RBEGamer/LixieClock/documentation/images/4_digit_complete.jpg

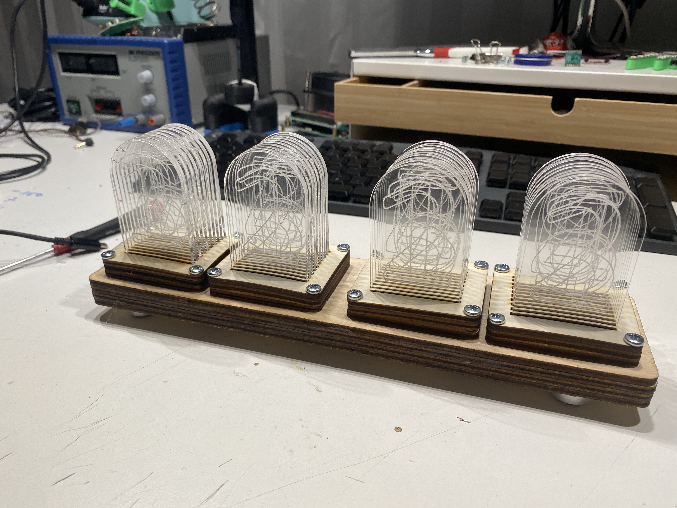
documentation/images/4_digit_complete.jpg
