RBEGamer/LixieClock/documentation/images/4_digit_on.jpg

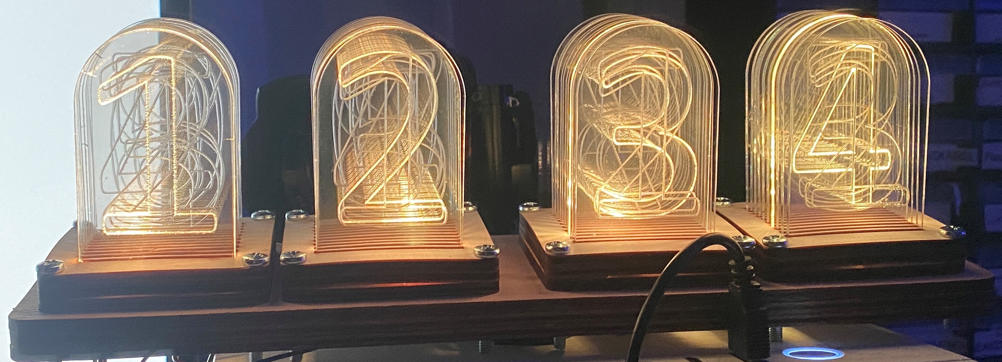
documentation/images/4_digit_on.jpg
