RBEGamer/LixieClock/documentation/images/2021-12-09 14.11.09.jpg

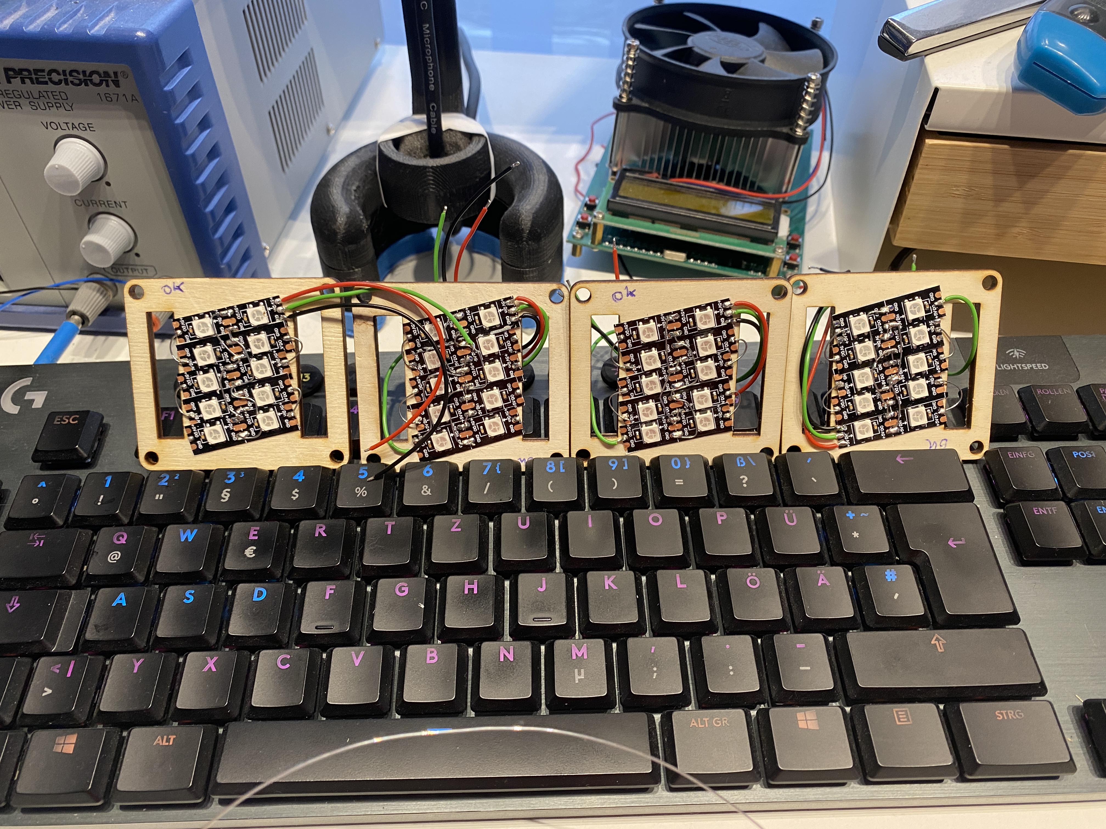
documentation/images/2021-12-09 14.11.09.jpg
