RBEGamer/LixieClock/documentation/images/2021-12-09 16.45.12-1.jpg

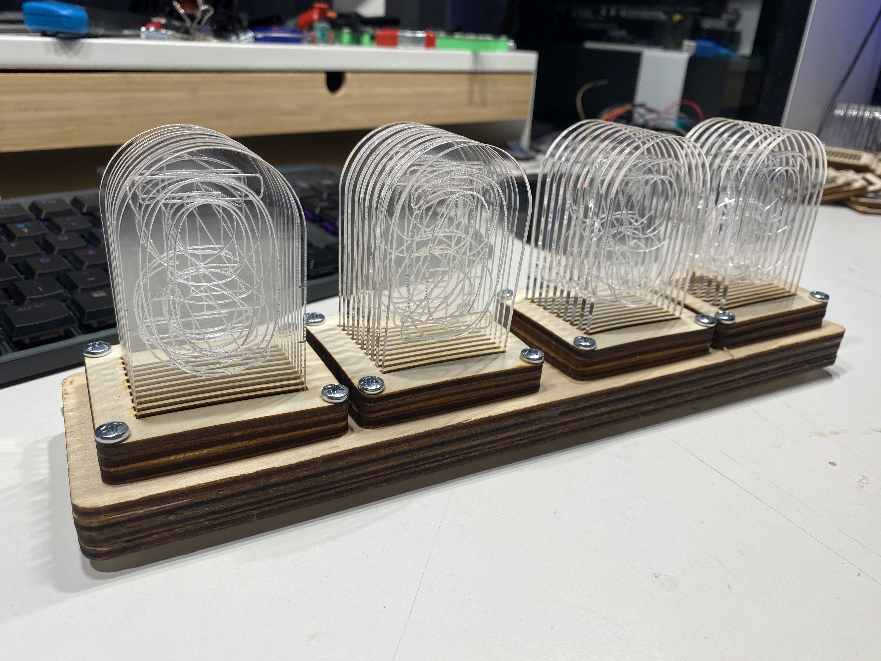
documentation/images/2021-12-09 16.45.12-1.jpg
