RBEGamer/LixieClock/documentation/images/2021-12-09 20.34.08.jpg

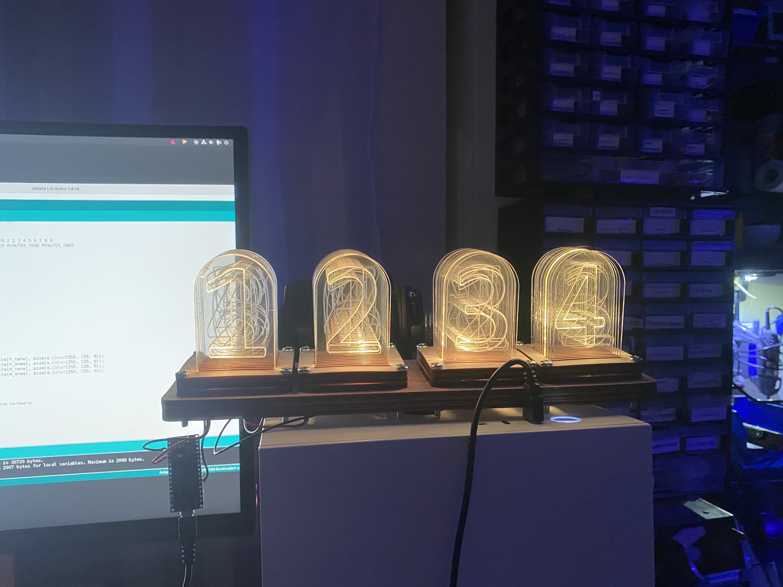
documentation/images/2021-12-09 20.34.08.jpg
