RBEGamer/LixieClock/documentation/images/2021-12-09 21.55.53.jpg

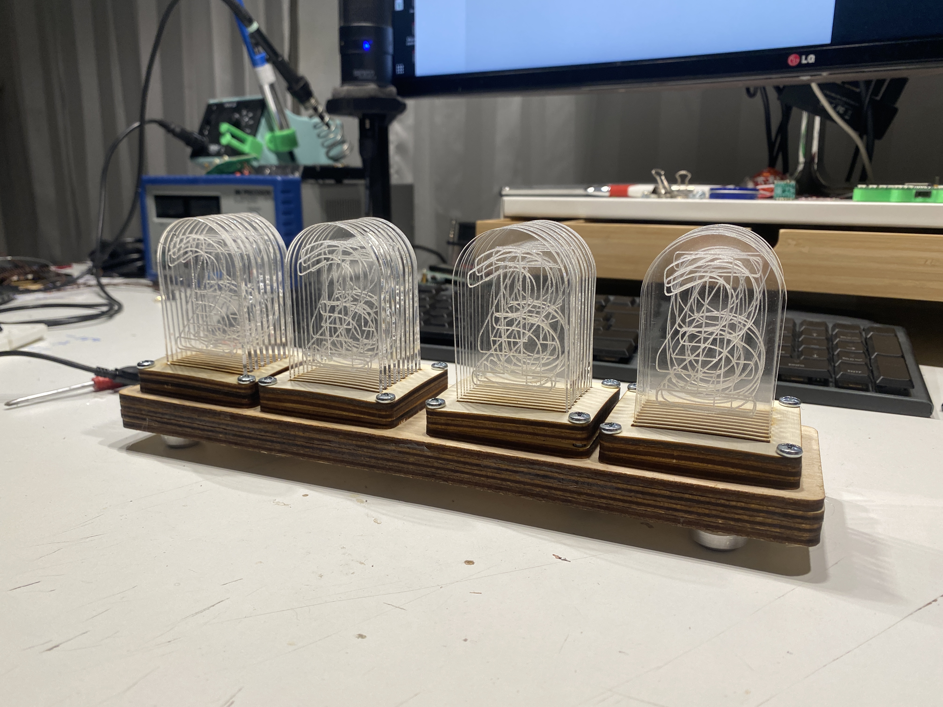
documentation/images/2021-12-09 21.55.53.jpg
