RBEGamer/LixieClock/documentation/images/2021-12-09 21.55.59.jpg

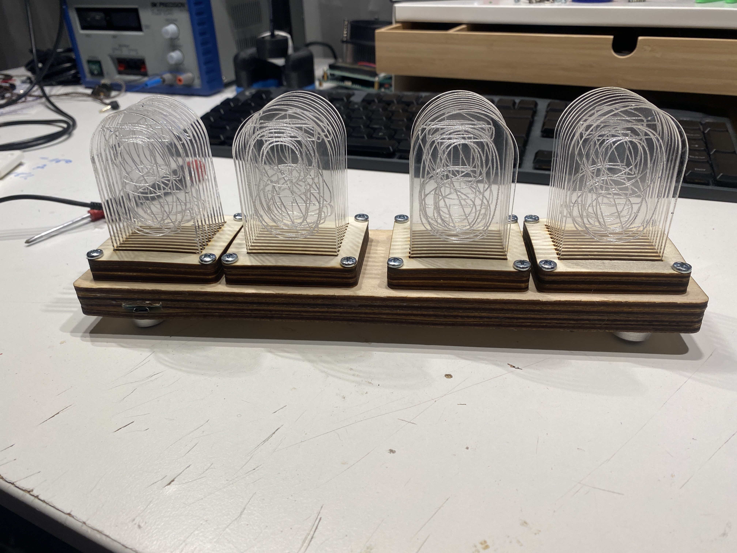
documentation/images/2021-12-09 21.55.59.jpg
