RBEGamer/LixieClock/documentation/images/2021-12-09 21.58.13.jpg

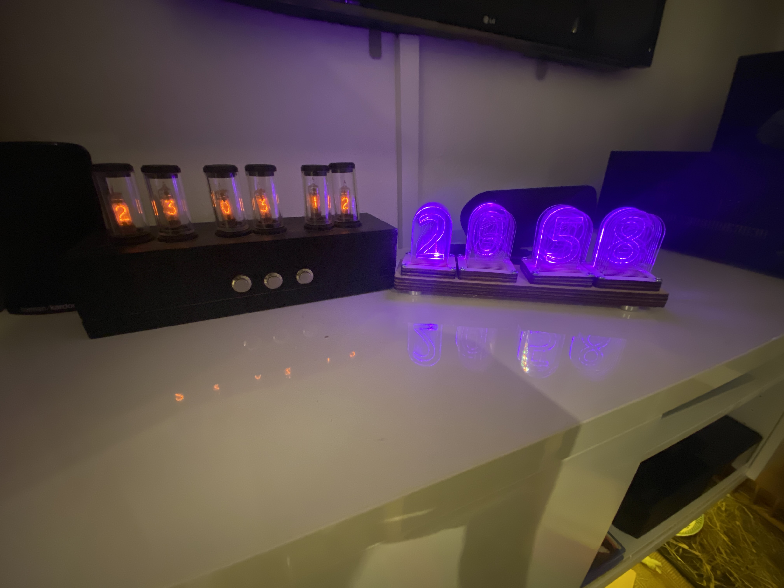
documentation/images/2021-12-09 21.58.13.jpg
