RBEGamer/LixieClock/documentation/images/2021-12-09 21.58.17.jpg

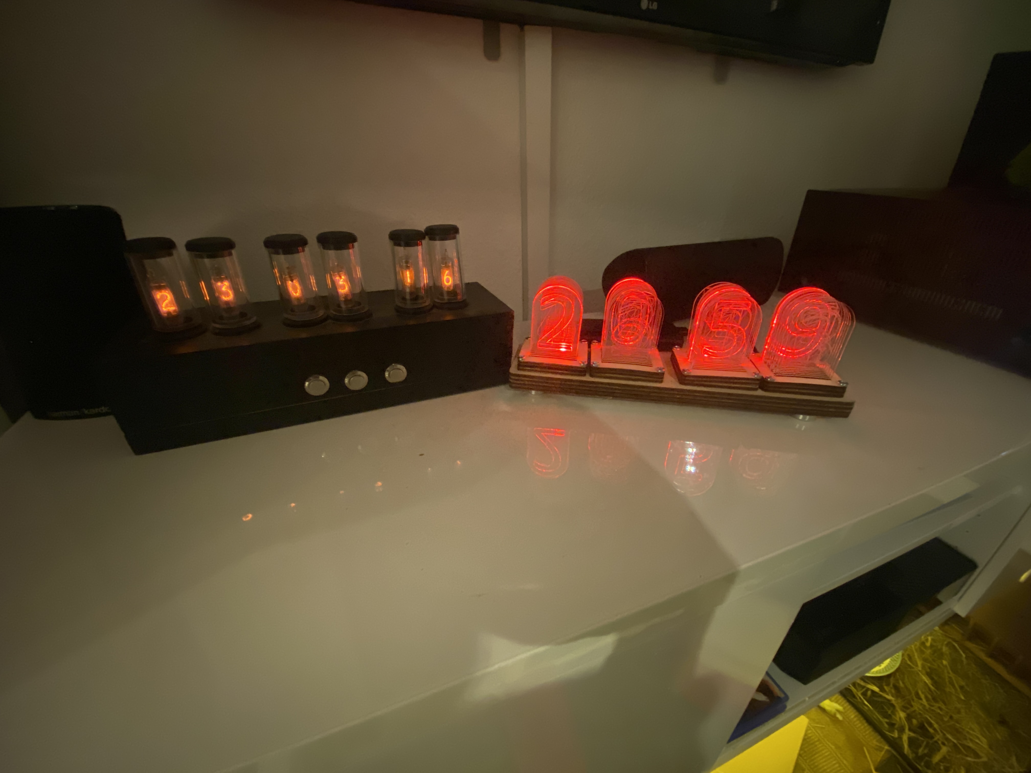
documentation/images/2021-12-09 21.58.17.jpg
