RBEGamer/LixieClock/documentation/images/2021-12-25 09.20.10.jpg

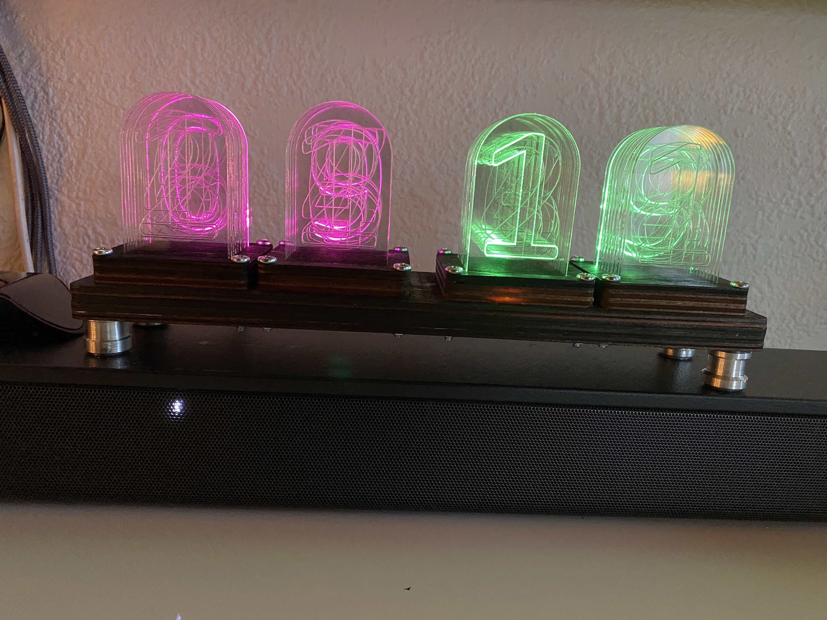
documentation/images/2021-12-25 09.20.10.jpg
