RBEGamer/LixieClock/documentation/images/2021-12-25 09.20.15.jpg

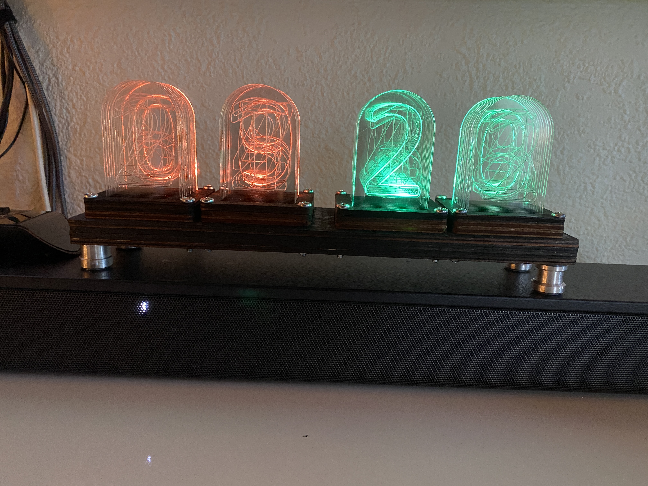
documentation/images/2021-12-25 09.20.15.jpg
