RBEGamer/LixieClock/documentation/images/single_digit.jpg

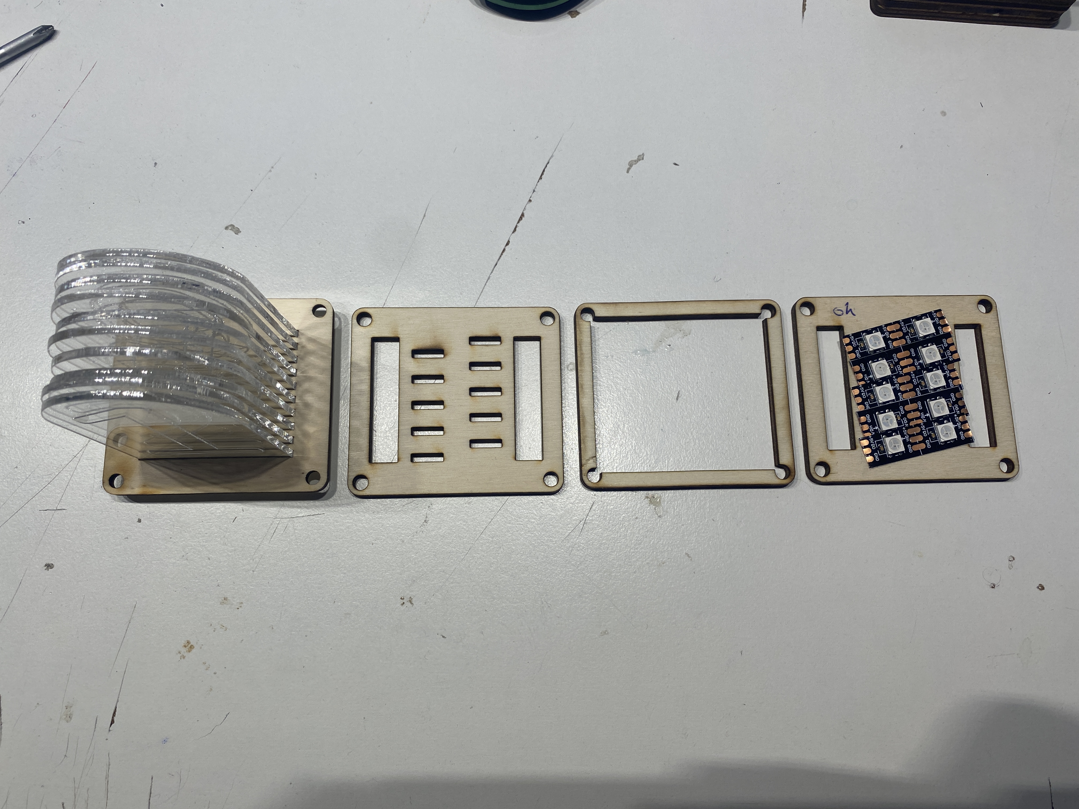
documentation/images/single_digit.jpg
