RBEGamer/LixieClock/documentation/images/single_digit_new.png

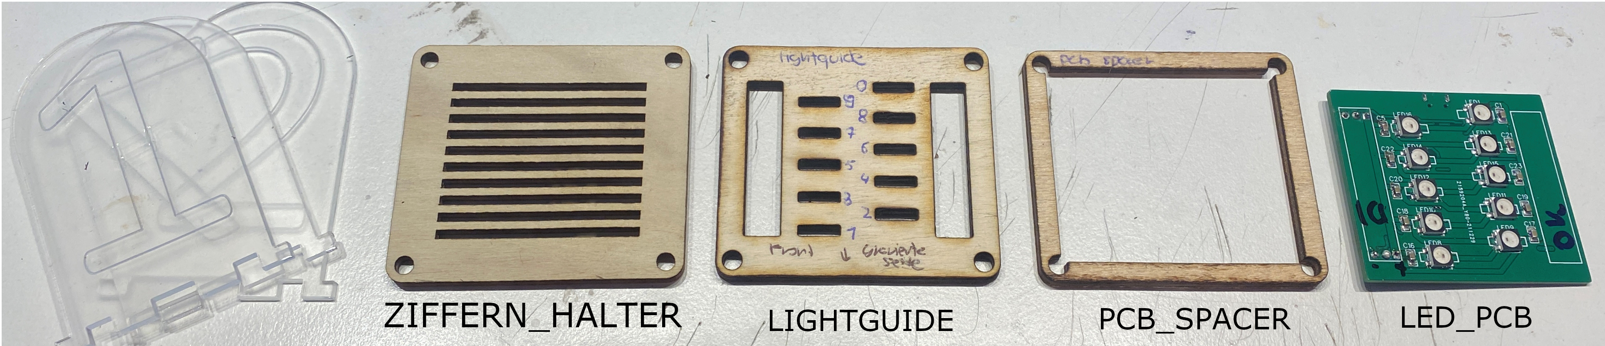
documentation/images/single_digit_new.png
