RBEGamer/LixieClock/src/pcb/LIXIE_PCB_V1/images/Screenshot from 2021-12-17 16-41-11.png

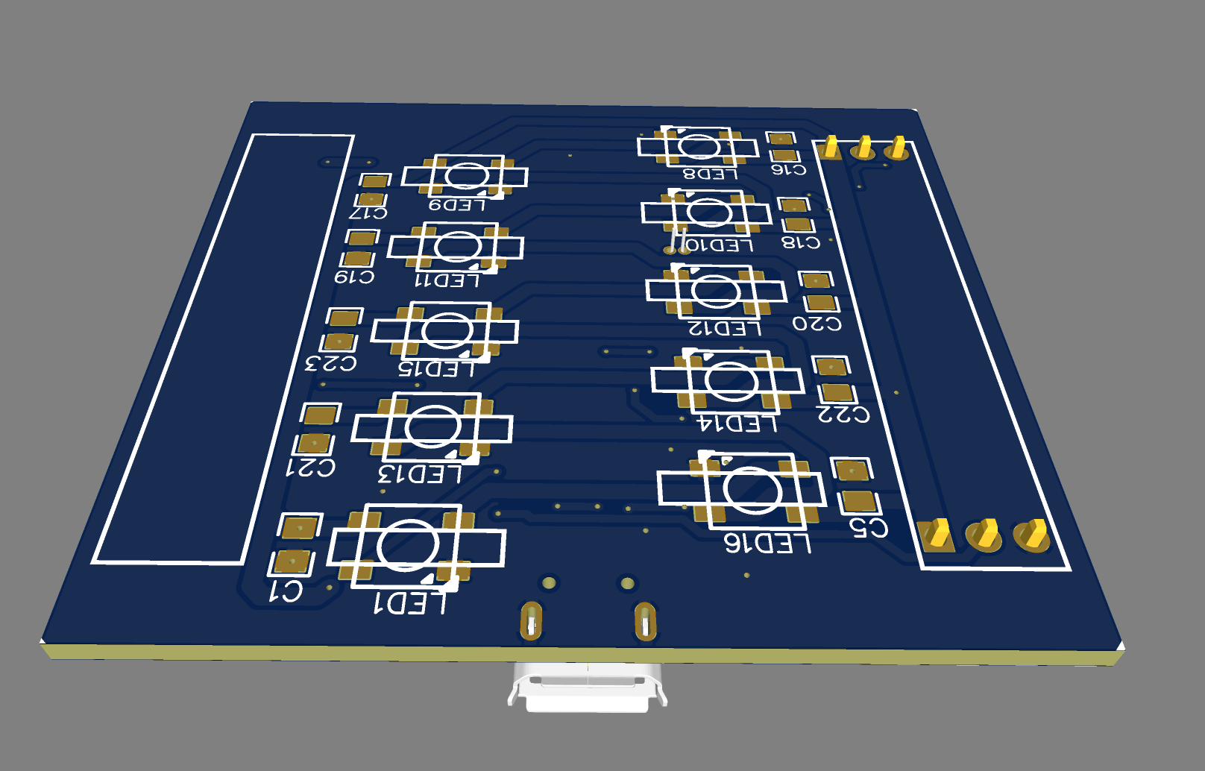
src/pcb/LIXIE_PCB_V1/images/Screenshot from 2021-12-17 16-41-11.png
