RBEGamer/LixieClock/src/svg/misc/casesize.PNG

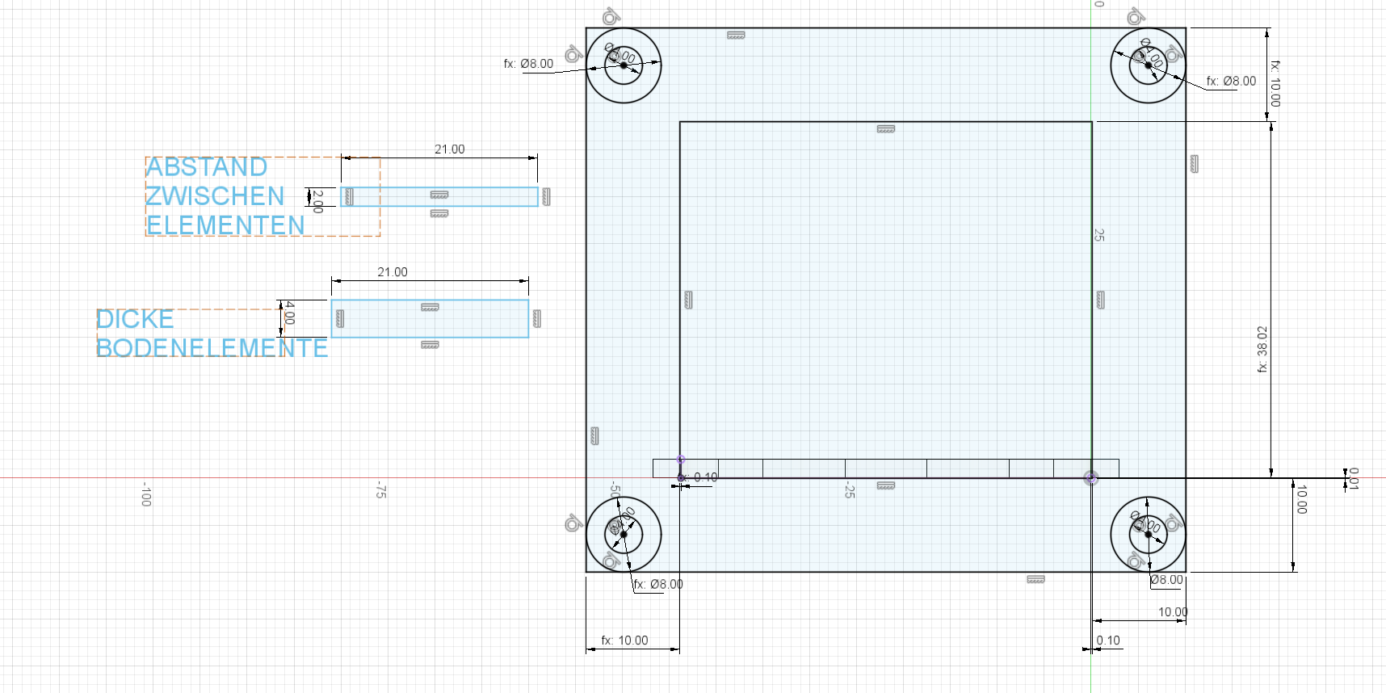
src/svg/misc/casesize.PNG
