RBEGamer/LixieClock/src/svg/misc/Unbenannt.PNG

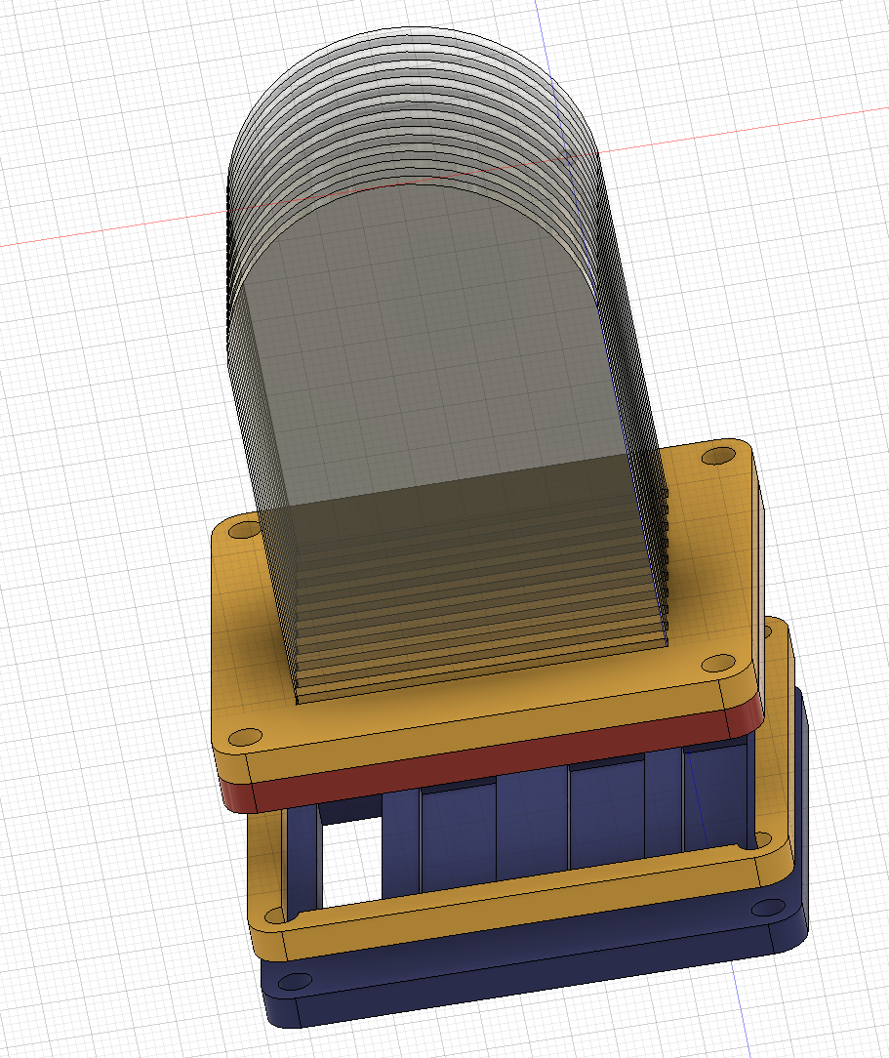
src/svg/misc/Unbenannt.PNG
