RBEGamer/LixieClock/src/svg/misc/zifferngrosse.PNG

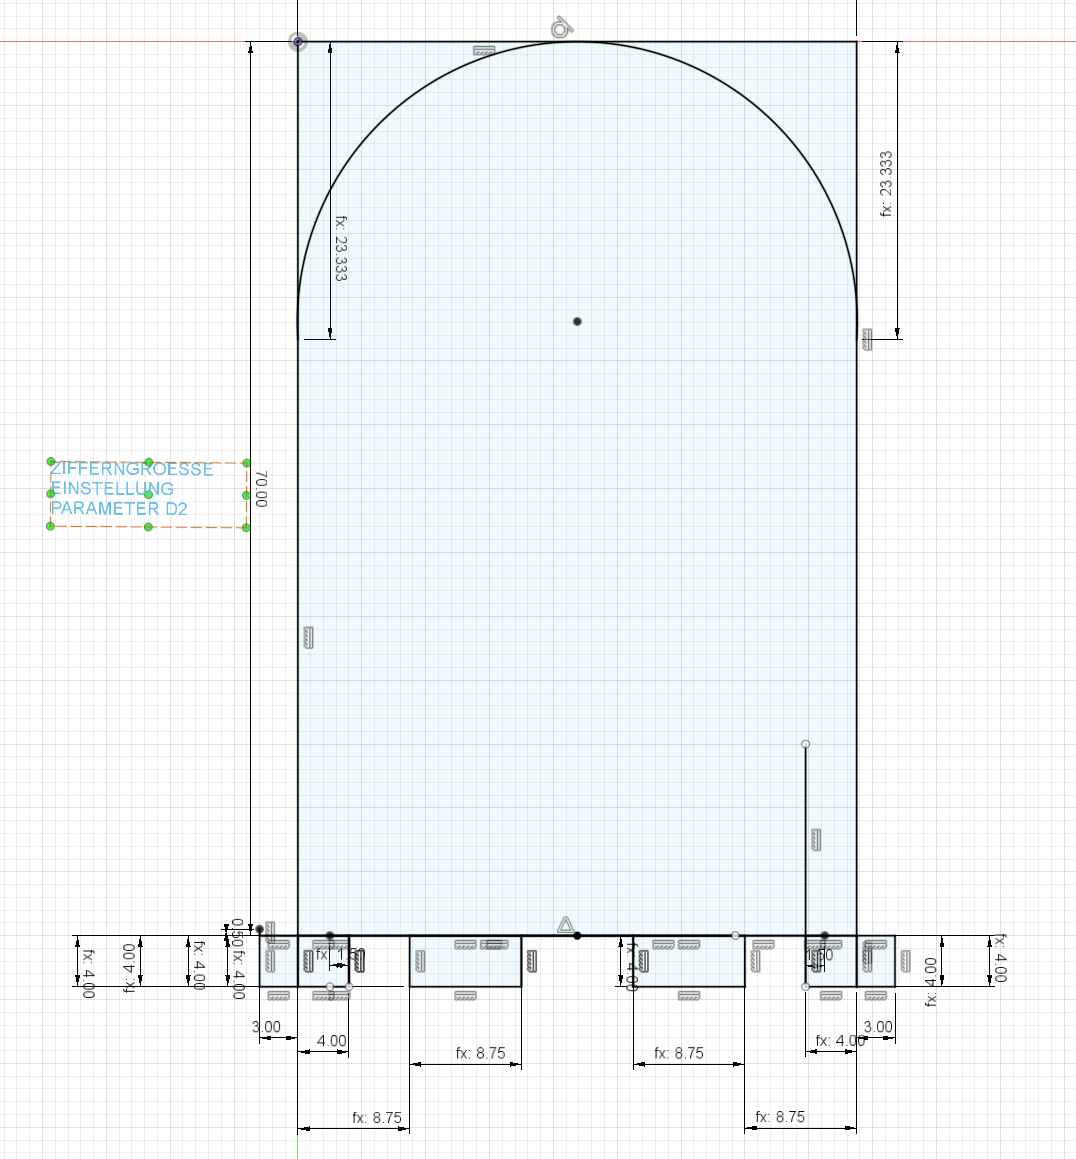
src/svg/misc/zifferngrosse.PNG
