RBEGamer/LixieClock/documentation/images/2021-12-09 16.19.54.jpg

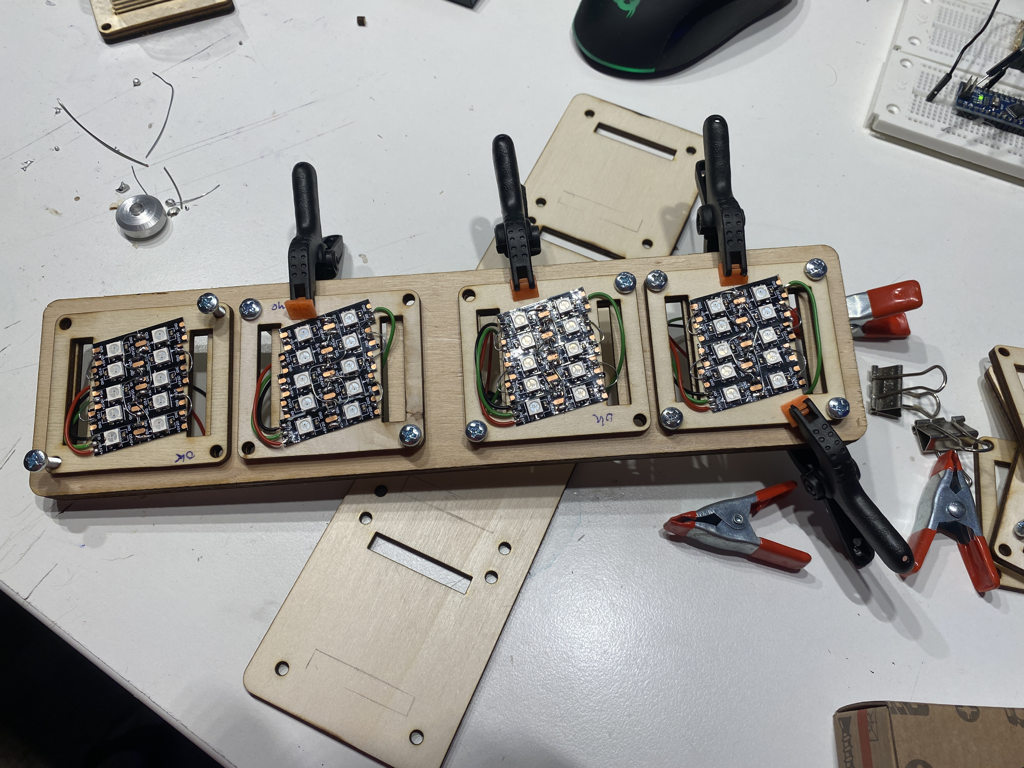
documentation/images/2021-12-09 16.19.54.jpg
