RBEGamer/LixieClock/documentation/images/2021-12-09 21.56.19.jpg

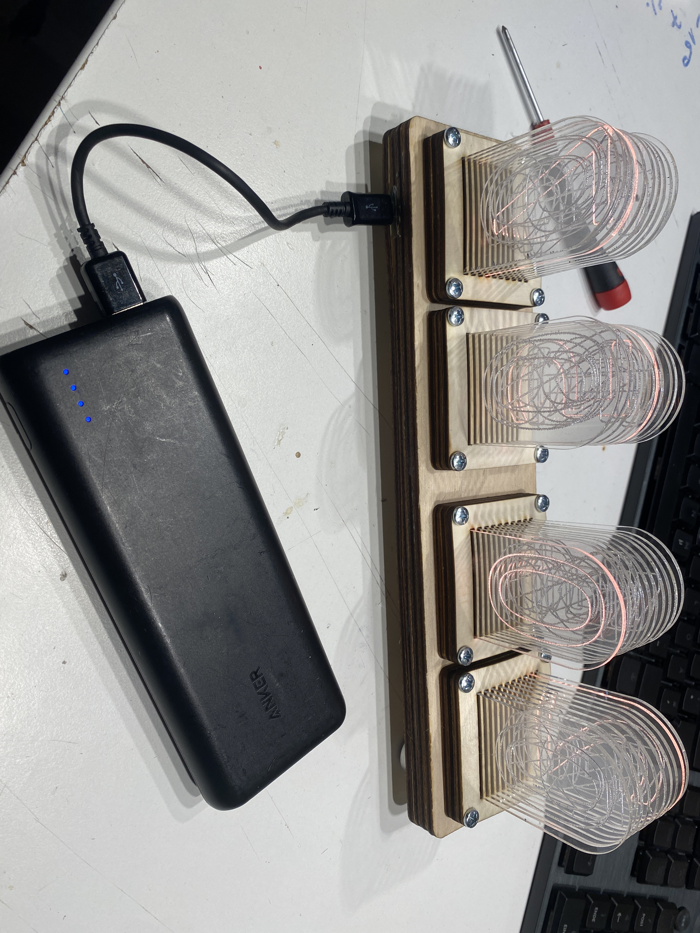
documentation/images/2021-12-09 21.56.19.jpg
