RBEGamer/LixieClock/documentation/images/2021-12-10 12.21.33.jpg

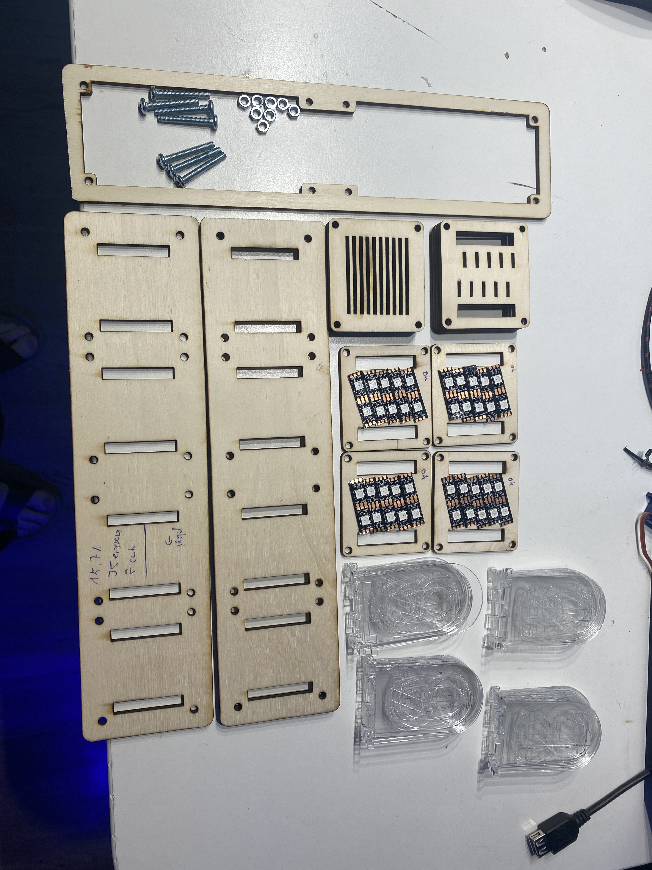
documentation/images/2021-12-10 12.21.33.jpg
