RBEGamer/LixieClock/documentation/images/2022-01-08 15.58.15.jpg

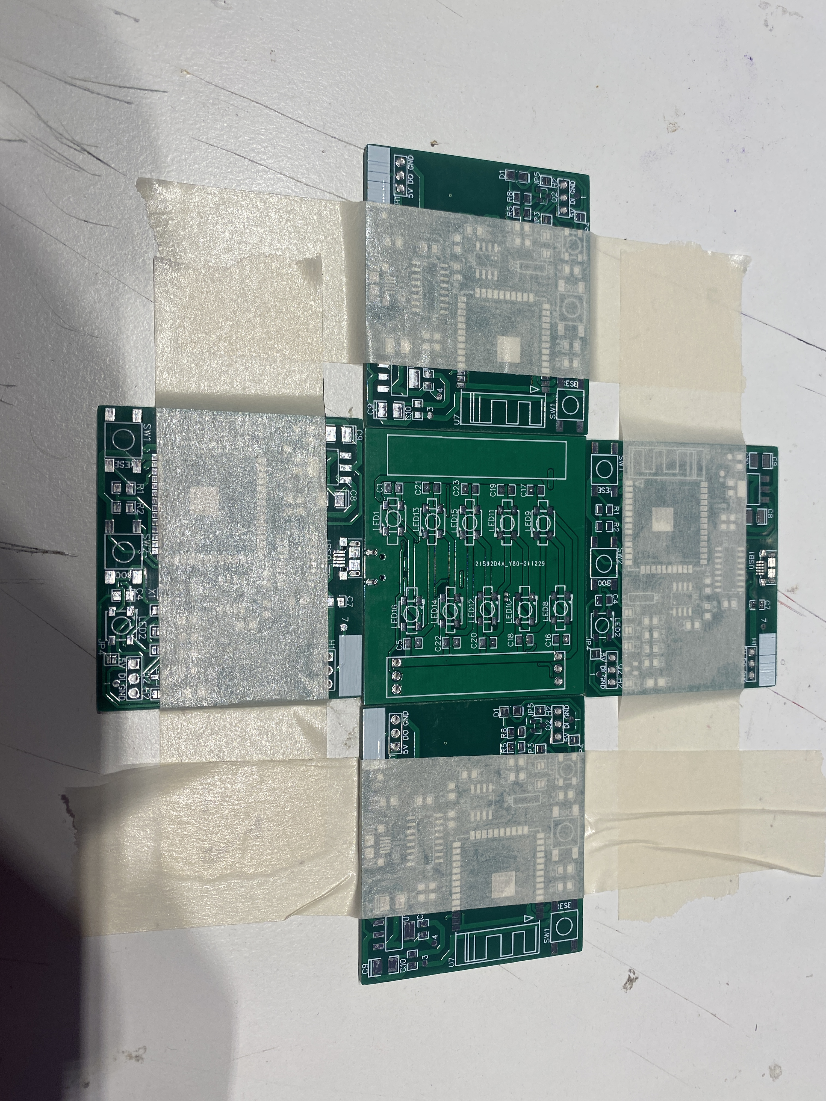
documentation/images/2022-01-08 15.58.15.jpg
